bauhausformandfunctionlab/covid19/Covid-19_Filters_for_Flutes/2020_11_01_FILTER_GRAND_FLUTE_360mm.pdf

MUSIC FILTERS FOR FLUTES
https://b.io/
2020-11-01 CC-BY-NC-SA

FILTER:
GROßE FLÖTE / GRAND FLUTE
L 360 x B 160 mm / 63°

DELETE ALL TEXT before lasercutting!
