bauhausformandfunctionlab/covid19/Covid-19_Filters_for_Flutes/2020_11_01_FILTER_PICCOLO_FLUTE_310mm.pdf

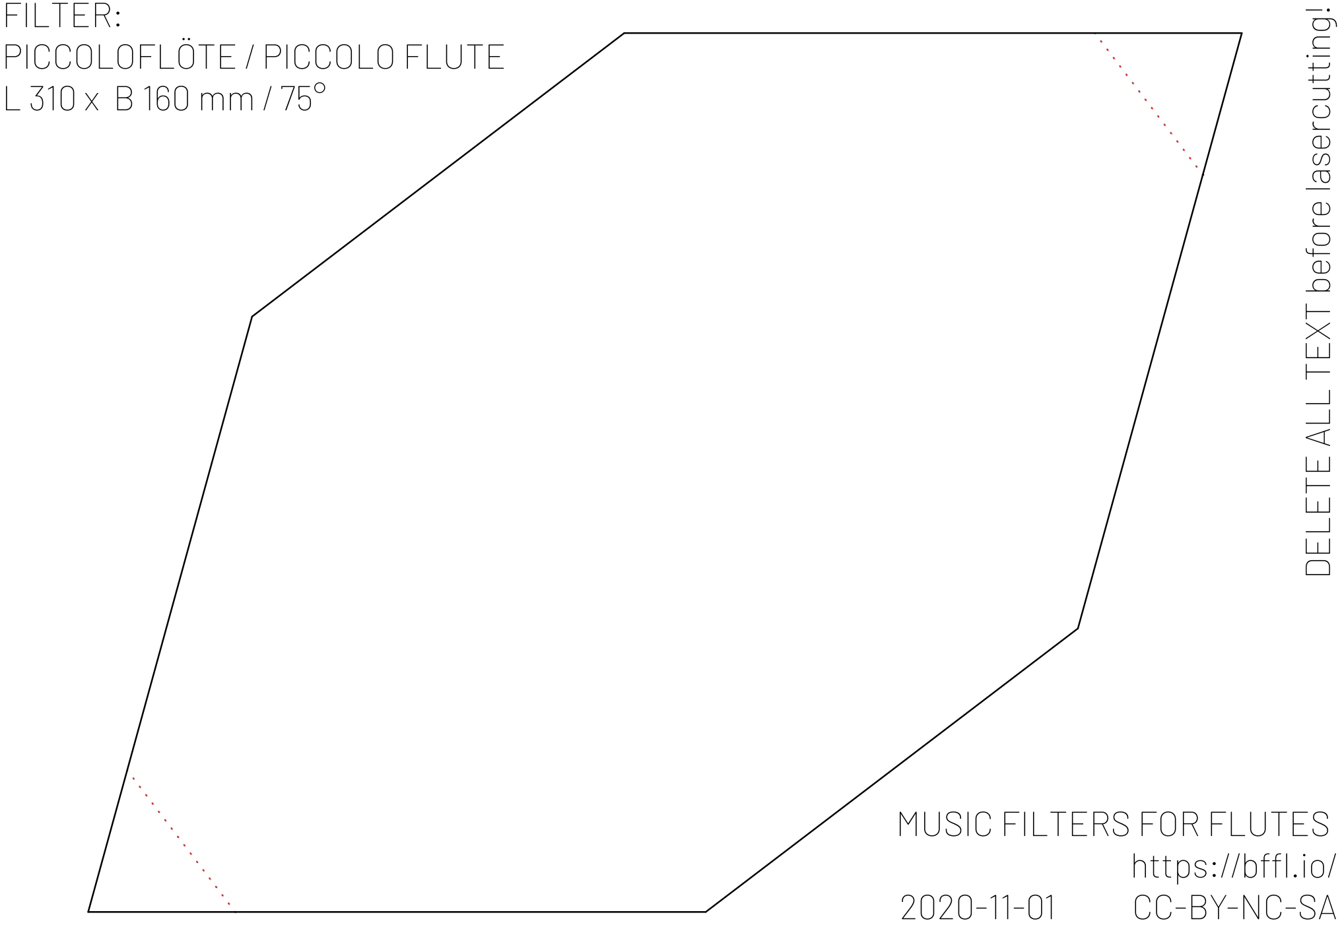
[picture p3: figure]
MUSIC FILTERS FOR FLUTES https://b.io/; PICCOLOFLÖTE / PICCOLO FLUTE L 310 x B 160 mm / 75; DELETE ALL TEXT before lasercutting!

FILTER:
