bauhausformandfunctionlab/covid19/Covid-19_Filters_for_Brass_Instruments/2020_09_08_FILTER_ALL_140-420mm.pdf

DELETE ALL TEXT before lasercutting!

MUSIC FILTERS FOR BRASS INSTRUMENTS 2020-09-08 https://b.io/
CC-BY-NC-SA

FILTER:
TUBA
HORN
TROMBONES
TRUMPET
Ø 140-420mm
