bauhausformandfunctionlab/covid19/Covid-19_Filters_for_Brass_Instruments/2020_09_08_FILTER_BASS_TROMBONE_245mm.pdf

DELETE ALL TEXT before lasercutting!

MUSIC FILTERS FOR BRASS INSTRUMENTS 2020-09-08 https://b.io/
CC-BY-NC-SA

FILTER:
BASS POSAUNE / BASS TROMBONE Ø 245 mm
