bauhausformandfunctionlab/covid19/Covid-19_Filters_for_Brass_Instruments/2020_09_08_FILTER_SIZES_TUBA_HORN_TROMBONE_TRUMPET.pdf

CUTOUT by HAND or LASER
DELETE ALL TEXT AND ARROWS before lasercutting!

MUSIC FILTERS FOR BRASS INSTRUMENTS 2020-09-08 https://b.io/
CC-BY-NC-SA

FILTER:
POSAUNE / TROMBONE
215 mm

FILTER:
TROMPETE / TRUMPET
140 mm

FILTER:
HORN / HORN
310 mm

FILTER:
TUBA / TUBA
420 mm

180.00mm

207.85mm

380.00mm

438.79mm

510.00mm

588.90mm | 317.54mm

275.00mm
