bauhausformandfunctionlab/covid19/Covid-19_Filters_for_Flutes/README_-_LICENSE_INFO_AND_DISCLAIMER.pdf

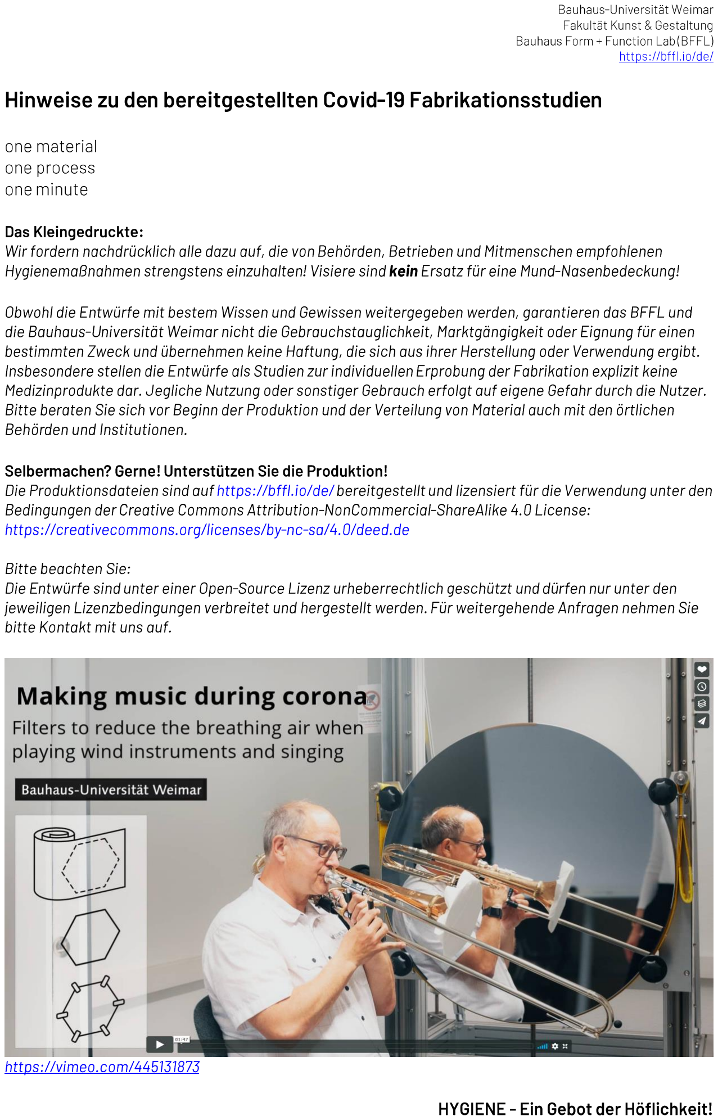
[picture p4: page 1]
