bauhausformandfunctionlab/covid19/BauhausUniVisor/BauhausUniVisor_Assembly_Guide.pdf

## BauhausUniVisor

## one material

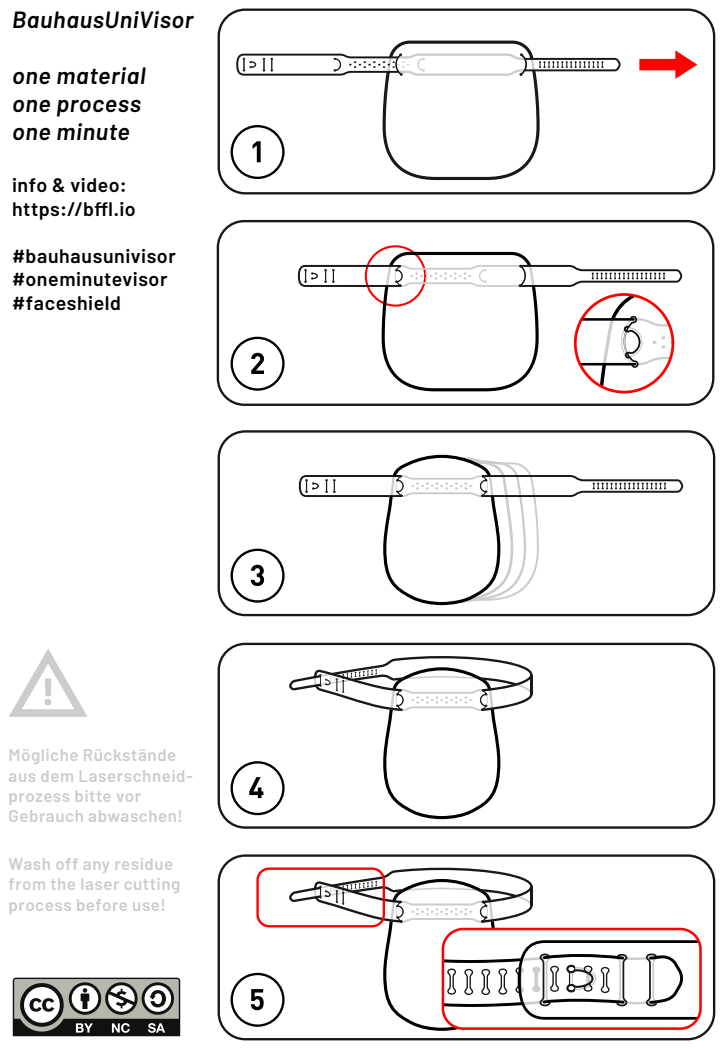
[picture p11: page 1]
one process one minute; info & video: https://b.io; #bauhausunivisor #oneminutevisor #faceshield

Mögliche Rückstände
aus dem Laserschneid-
prozess bitte vor
Gebrauch abwaschen!

Wash off any residue
from the laser cutting
process before use!
