bauhausformandfunctionlab/covid19/Covid-19_Filters_for_Brass_Instruments/2020_09_08_FILTER_SIZES_TUBA_HORN_TROMBONE_TRUMPET_with_TAPE_MARKINGS.pdf

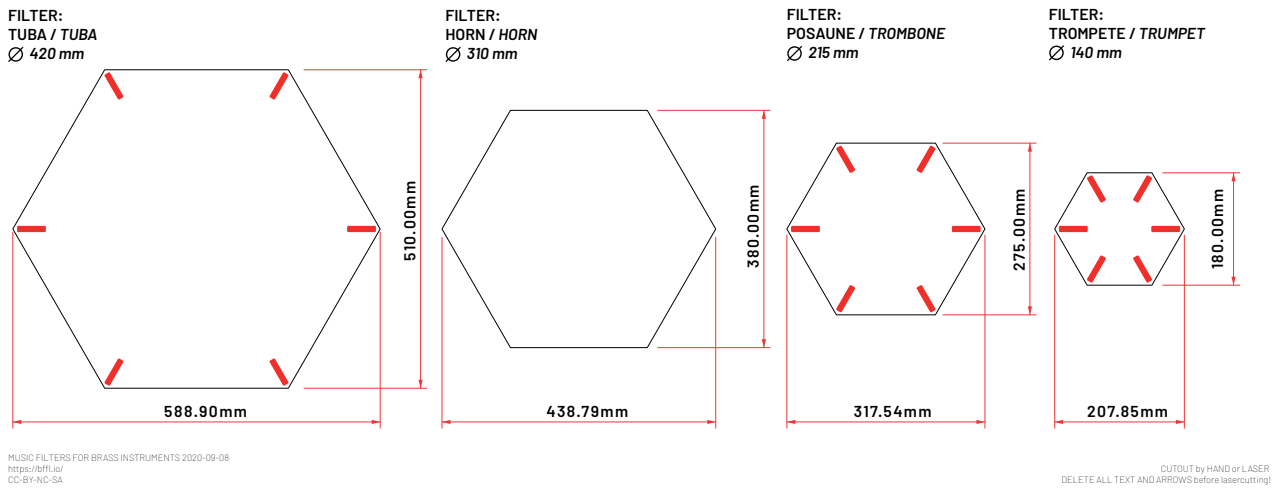
[picture p12: page 1]
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

MUSIC FILTERS FOR BRASS INSTRUMENTS 2020-09-08
https://b.io/

CUTOUT by HAND or LASER

DELETE ALL TEXT AND ARROWS before lasercutting!
