bauhausformandfunctionlab/covid19/BauhausUniVisor/BauhausUniVisor_2020_04_16_VARIANT_A_and_VARIANT_B_combined_NO_BRIDGES.pdf

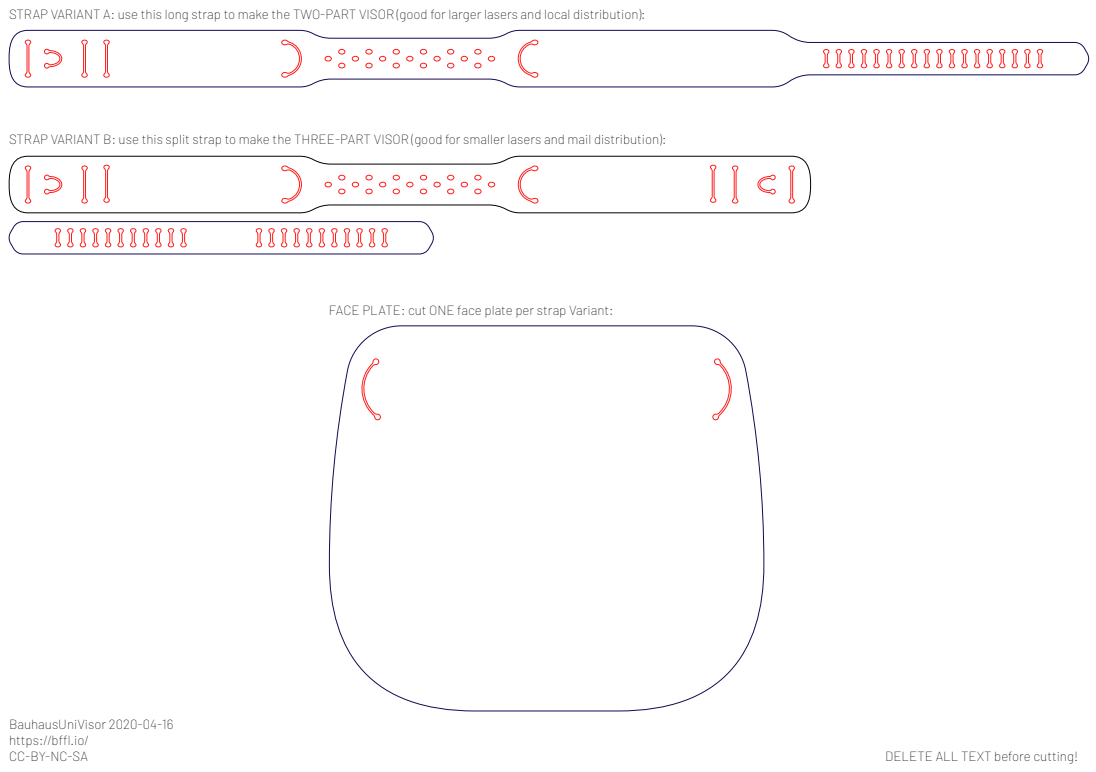
[picture p13: page 1]

STRAP VARIANT A: use this long strap to make the TWO-PART VISOR (good for larger lasers and local distribution):

STRAP VARIANT B: use this split strap to make the THREE-PART VISOR (good for smaller lasers and mail distribution):

FACE PLATE: cut ONE face plate per strap Variant:

BauhausUniVisor 2020-04-16
https://b.io/

DELETE ALL TEXT before cutting!
