bauhausformandfunctionlab/covid19/BauhausUniVisor/pre-arranged production layouts for specific laser cutter sizes/2020_04_09_TWO_VISORS_AND_STRAPS_with_0.8mm_BRIDGES_for_600x400mm_Lasers_PET_40W_singlepass_50perc_30mm-sec_for_BEAMBOX_PRO.pdf

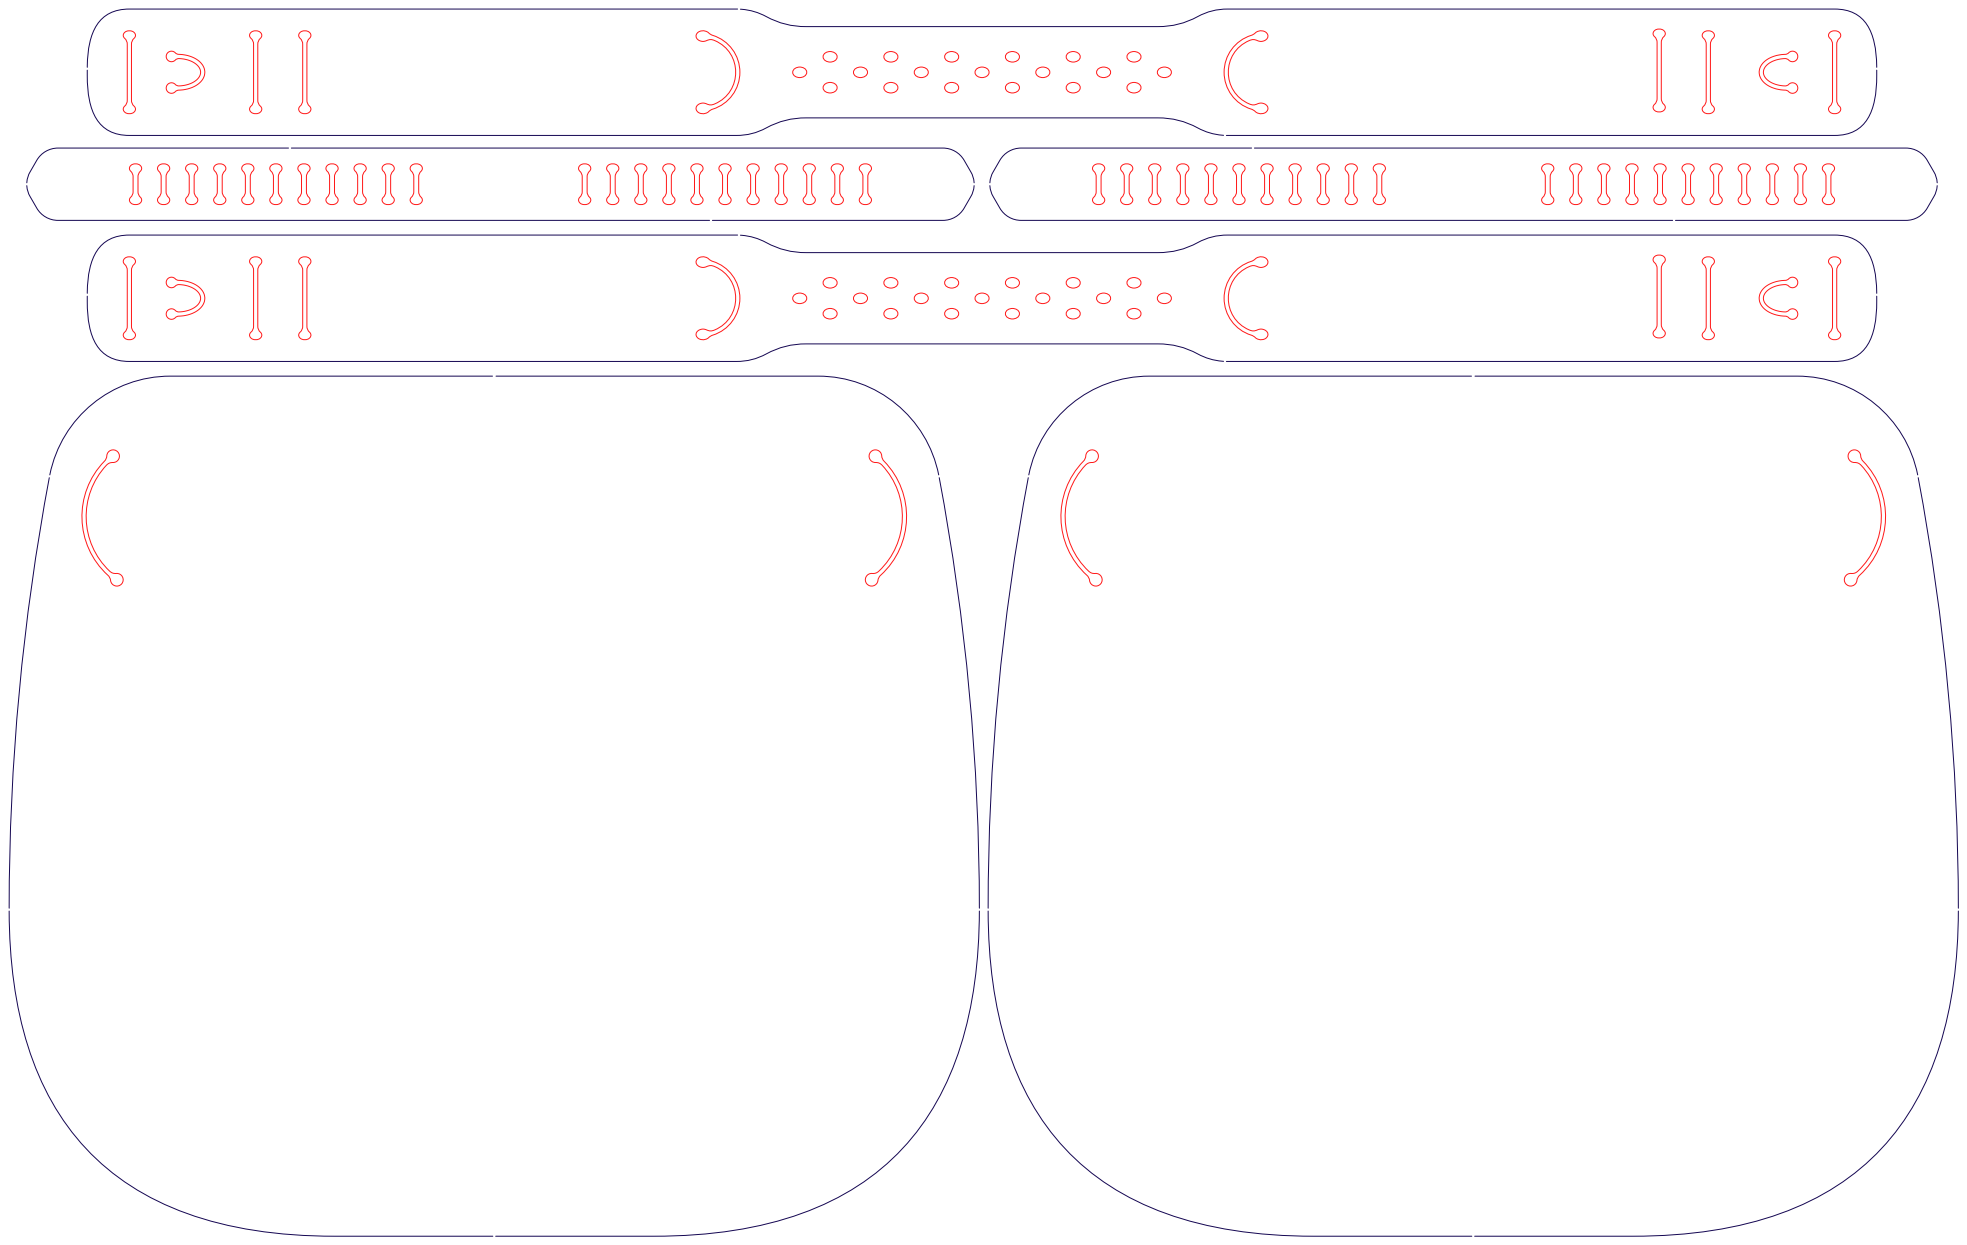
[picture p20: page 1]
