bauhausformandfunctionlab/covid19/BauhausUniVisor/pre-arranged production layouts for specific laser cutter sizes/2020_04_16_VARIANT_A_TWO_PART_VISOR_NO_BRIDGES.pdf

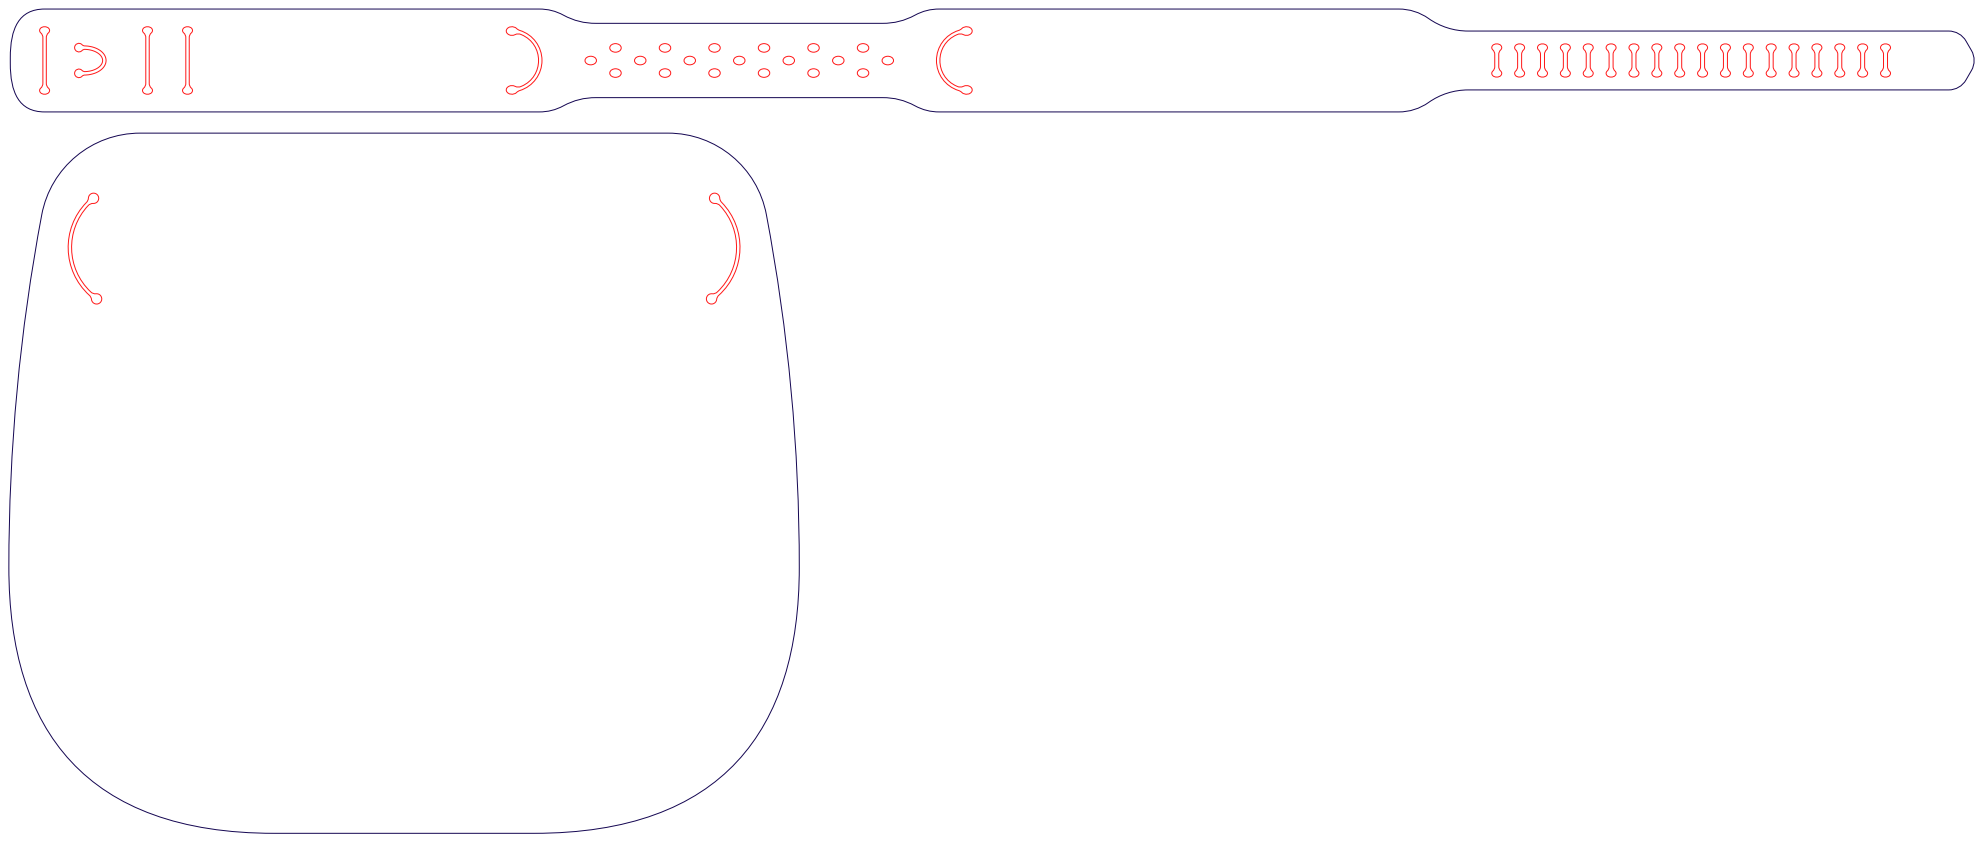
[picture p21: page 1]
