bauhausformandfunctionlab/covid19/BauhausUniVisor/pre-arranged production layouts for specific laser cutter sizes/2020_04_16_VARIANT_B_THREE_PART_VISOR_with_0.8mm_BRIDGES.pdf

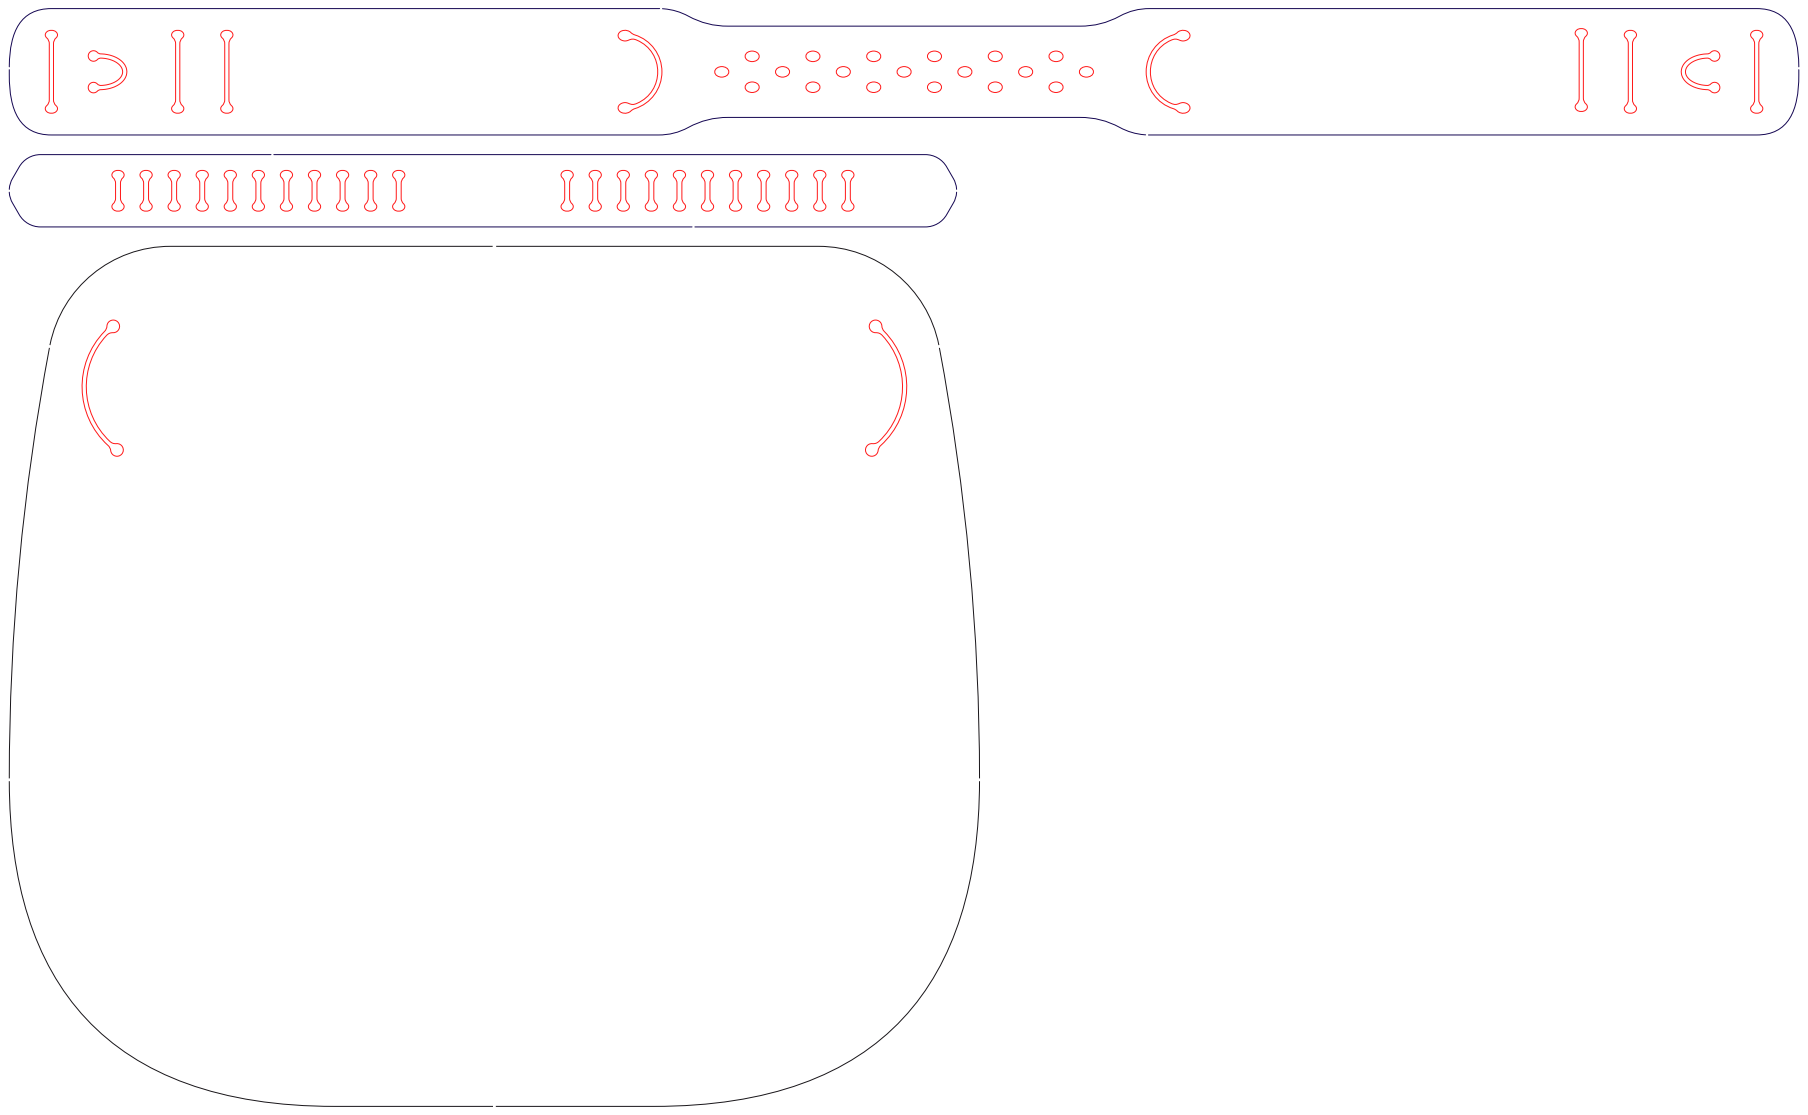
[picture p22: page 1]
