bauhausformandfunctionlab/covid19/BauhausUniVisor/pre-arranged production layouts for specific laser cutter sizes/2020_04_07_EIGHT_FACEPLATES_NO_STRAPS_for_1000x600mm_Lasers.pdf

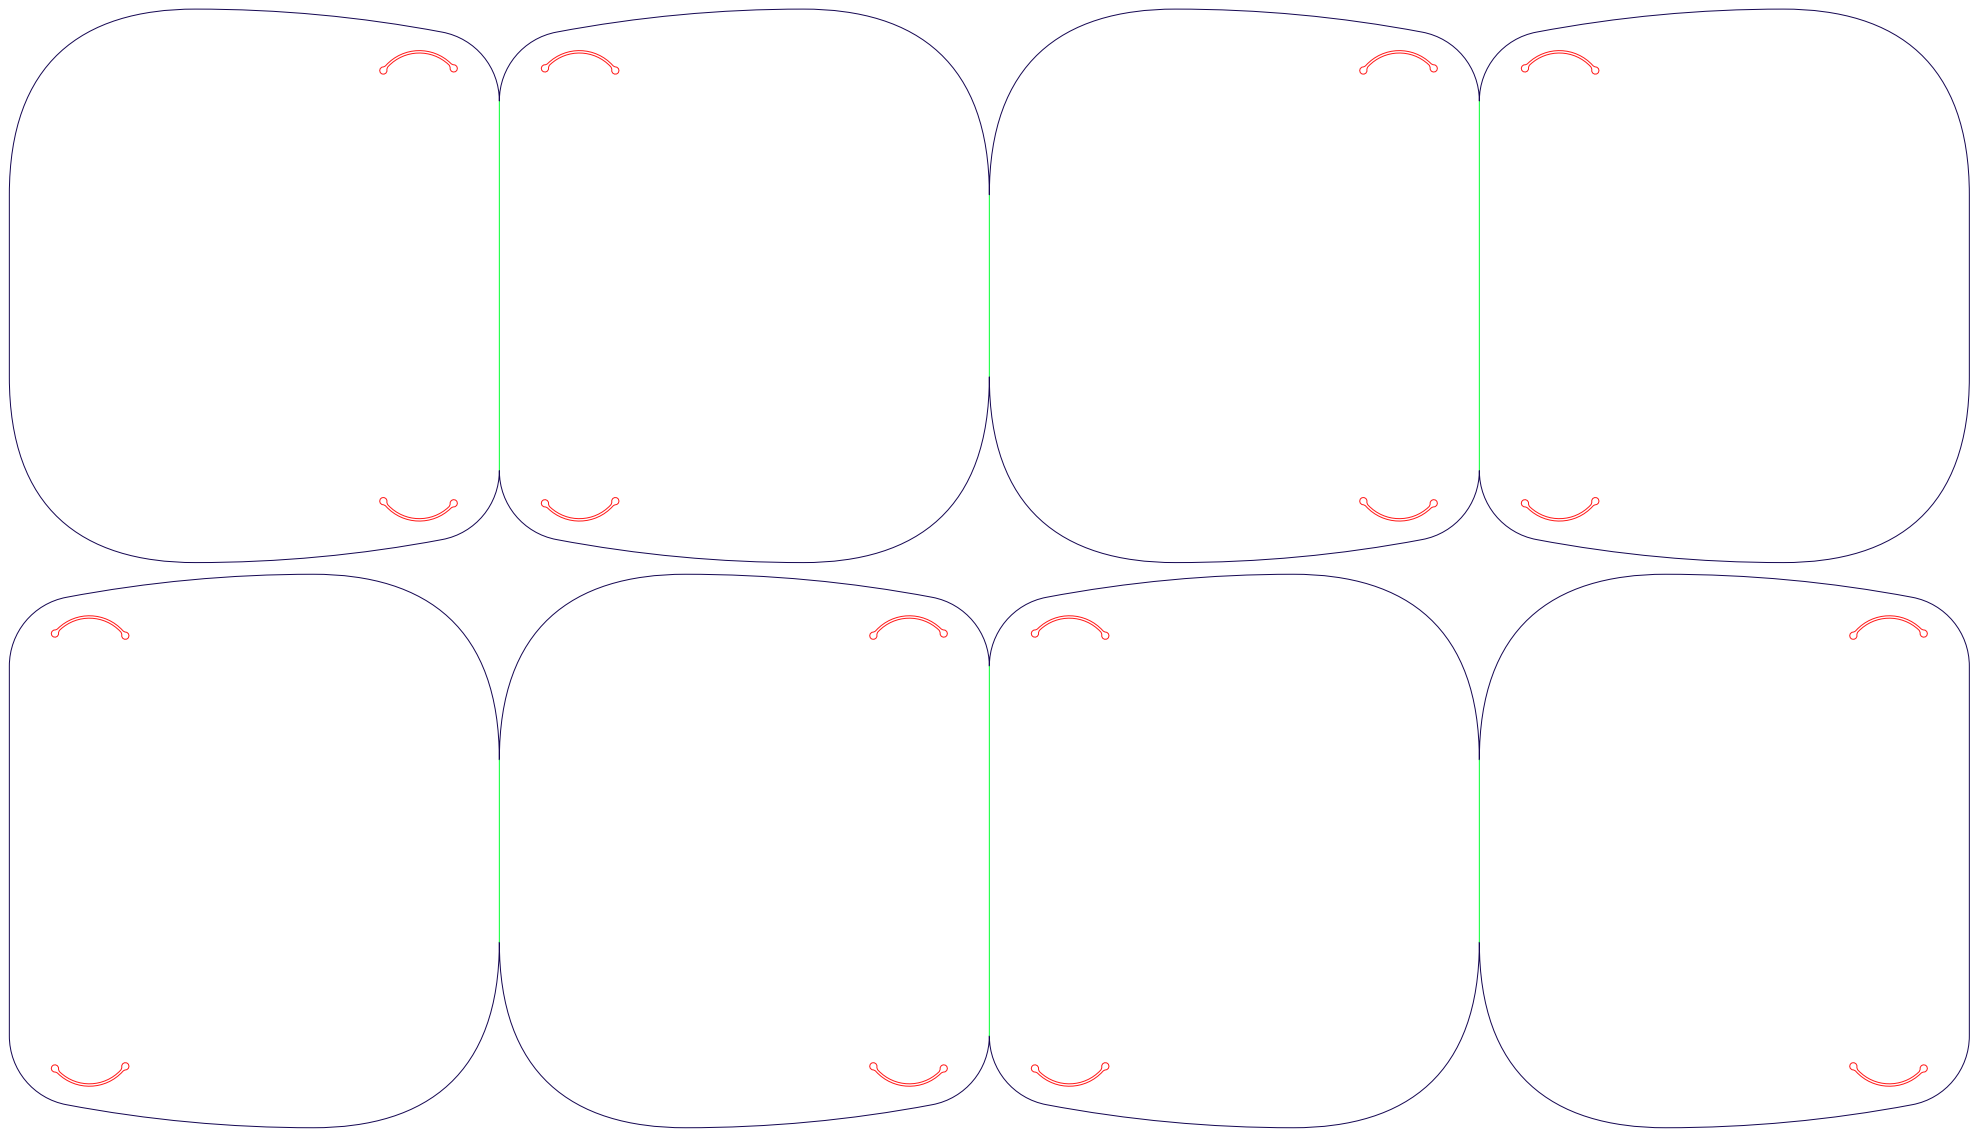
[picture p23: page 1]
