bauhausformandfunctionlab/covid19/BauhausUniVisor/coburg/2020_04_15_PRODUCTION_FILE_for_1000x430mm_PET_SHEETS_with_BRIDGES.pdf

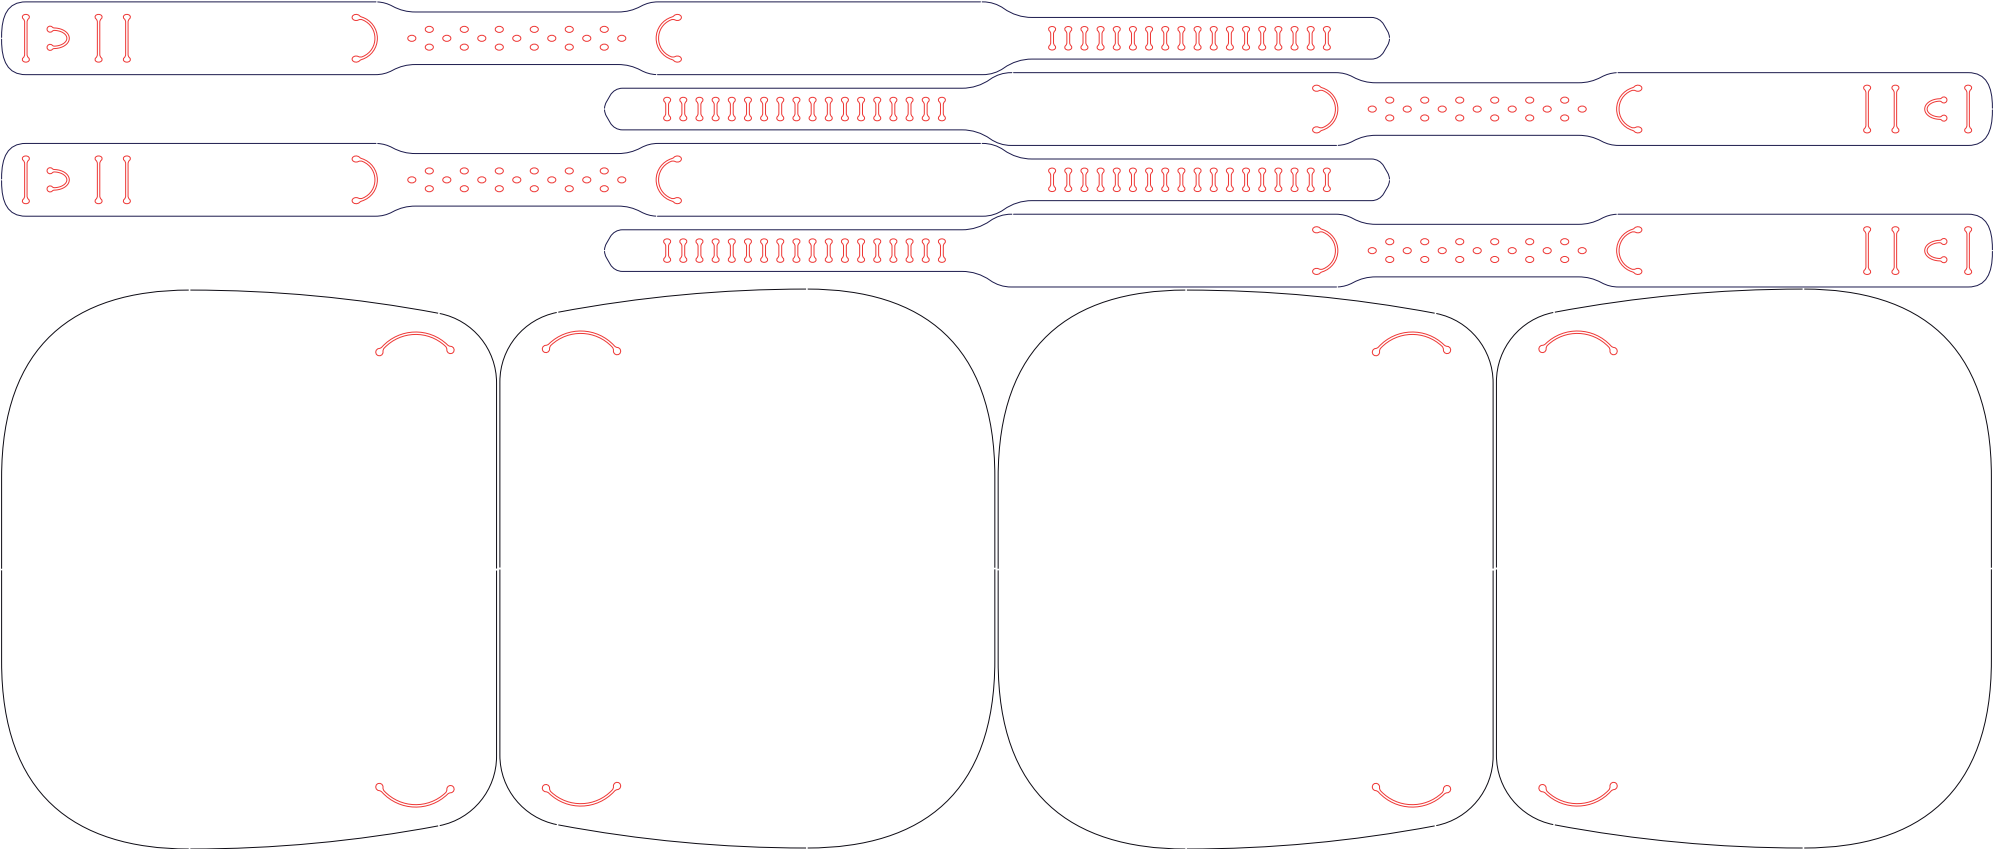
[picture p24: page 1]
