bauhausformandfunctionlab/covid19/BauhausUniVisor/coburg/2020_04_15_PRODUCTION_FILE_for_840x430mm_PET_SHEETS_02_with_BRIDGES.pdf

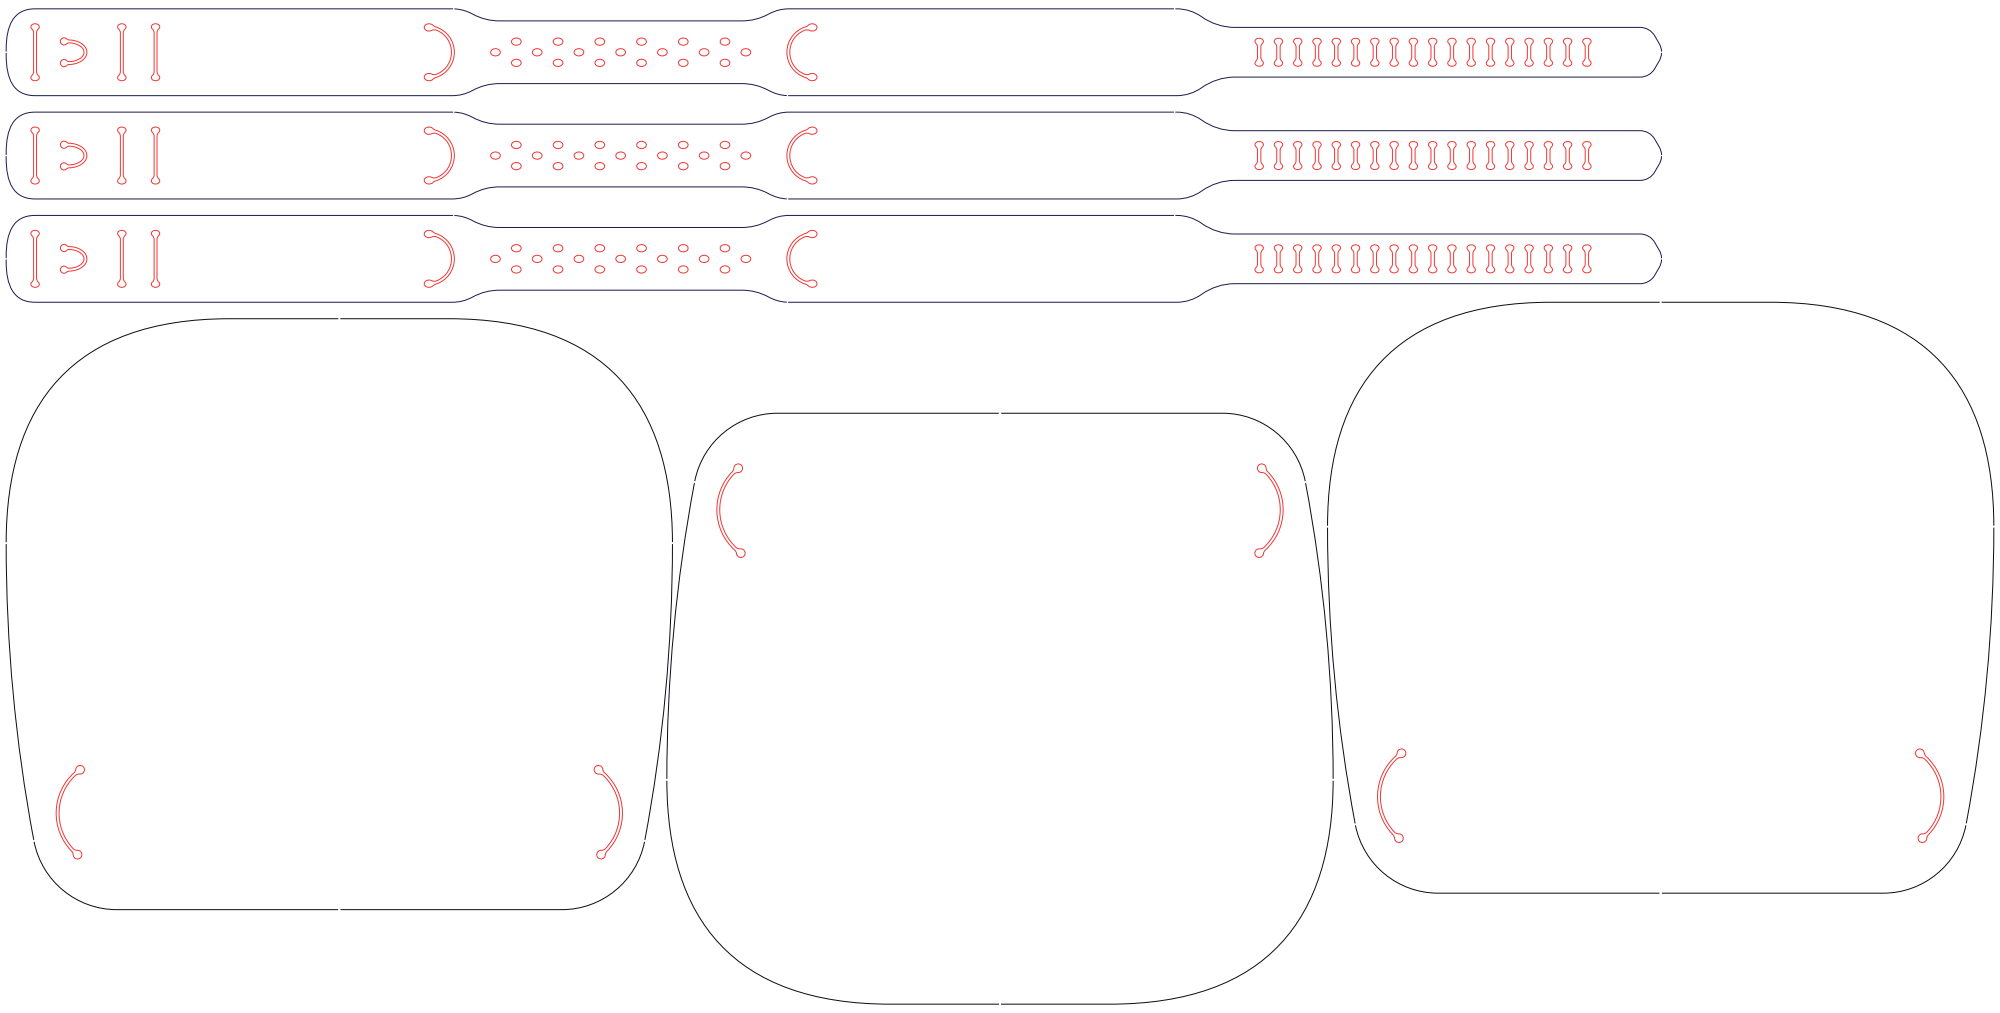
[picture p25: page 1]
